8n1/ESP8266-Breakout-Adapter/Breakout Adapter v3/ESP Breakout Adapter v3.0A - AS1363 - Mini/ESP Breakout Adapter - v3_0A - AS1363 - Mini_sch.png

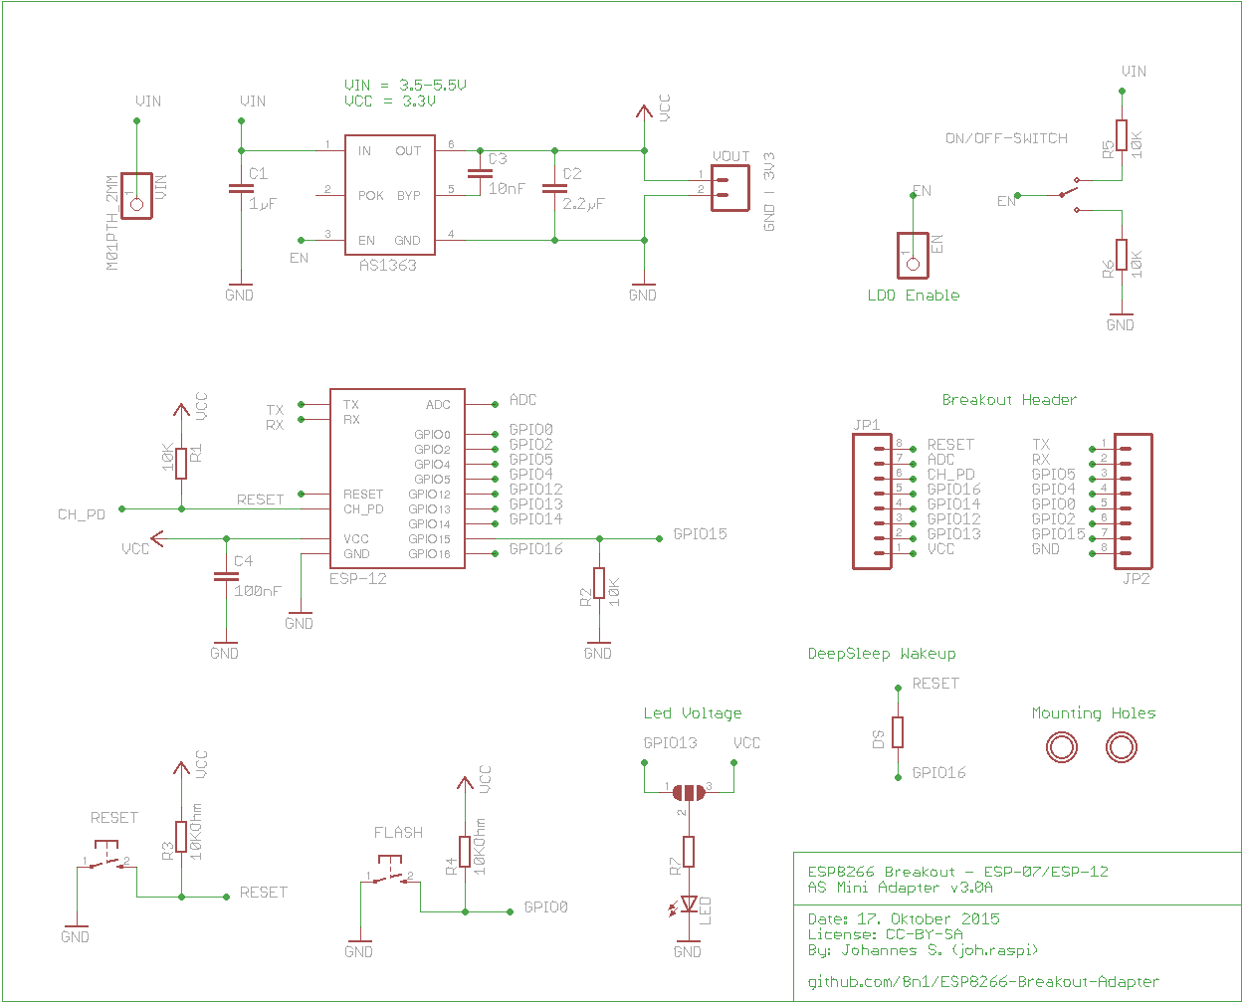
Breakout Adapter v3/ESP Breakout Adapter v3.0A - AS1363 - Mini/ESP Breakout Adapter - v3_0A - AS1363 - Mini_sch.png
