8n1/ESP8266-Breakout-Adapter/Breakout Adapter v3/ESP Breakout Adapter v3.0A - AS1363 - Mini/oshpark renderings/b_ohspark - board bottom_b.png

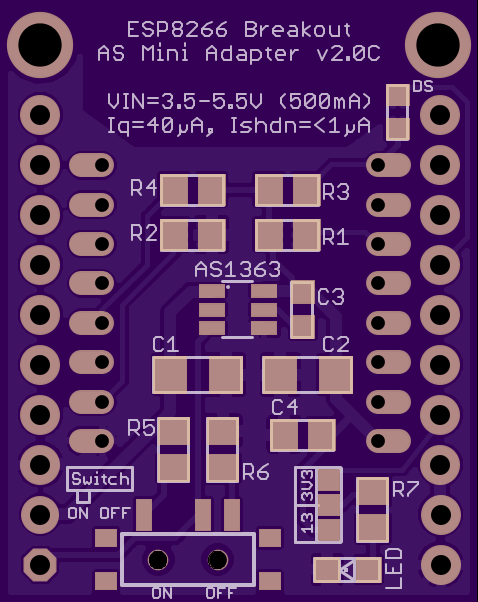
Breakout Adapter v3/ESP Breakout Adapter v3.0A - AS1363 - Mini/oshpark renderings/b_ohspark - board bottom_b.png
