8n1/ESP8266-Breakout-Adapter/Breakout Adapter v3/ESP Breakout Adapter v3.0A - AS1363 - Mini/oshpark renderings/oshpark - bottom layer.png

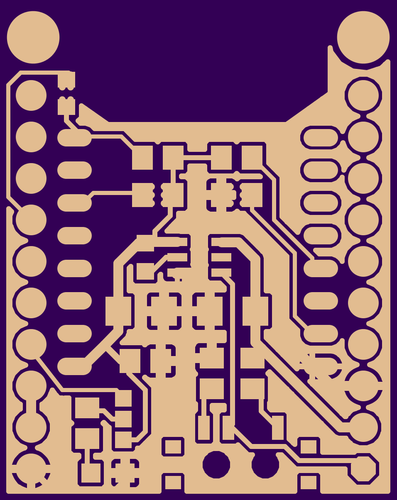
Breakout Adapter v3/ESP Breakout Adapter v3.0A - AS1363 - Mini/oshpark renderings/oshpark - bottom layer.png
