8n1/ESP8266-Breakout-Adapter/Breakout Adapter v3/ESP Breakout Adapter v3.1A - AS1363 - Mini/ESP Breakout Adapter - v3_1A - AS1363 - Mini_sch.png

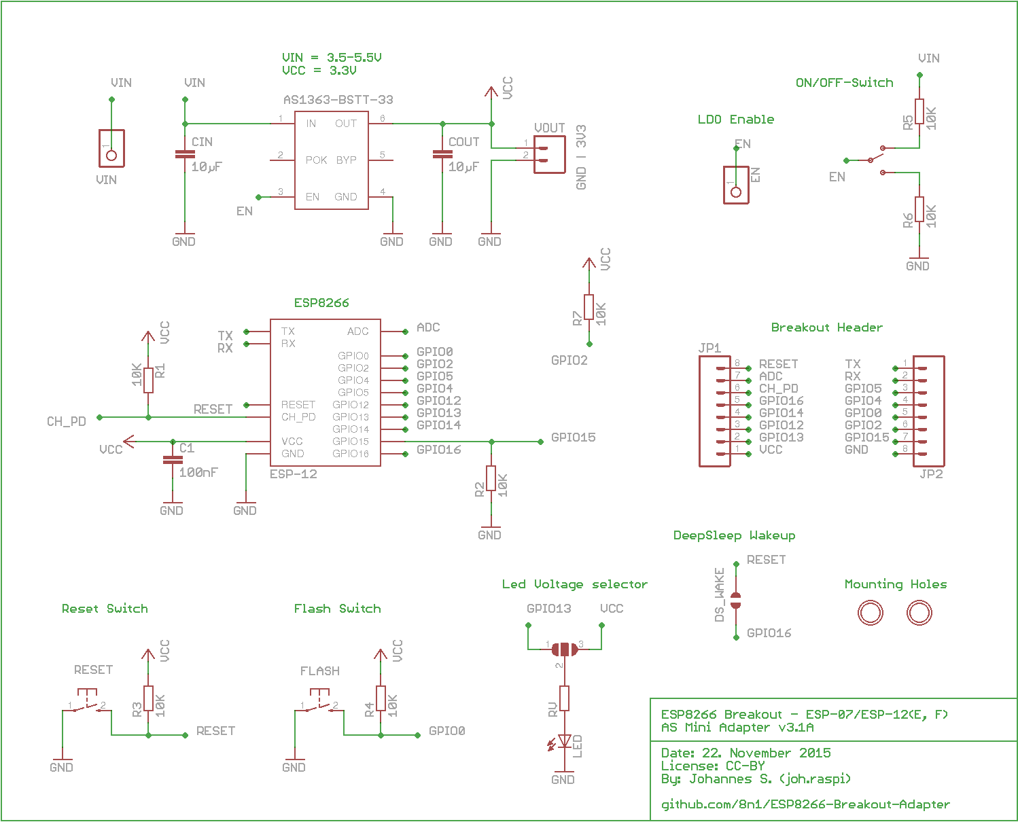
Breakout Adapter v3/ESP Breakout Adapter v3.1A - AS1363 - Mini/ESP Breakout Adapter - v3_1A - AS1363 - Mini_sch.png
