8n1/ESP8266-Breakout-Adapter/Breakout Adapter v3/ESP Breakout Adapter v3.1A - AS1363 - Mini/oshpark renderings/Board_Top.png

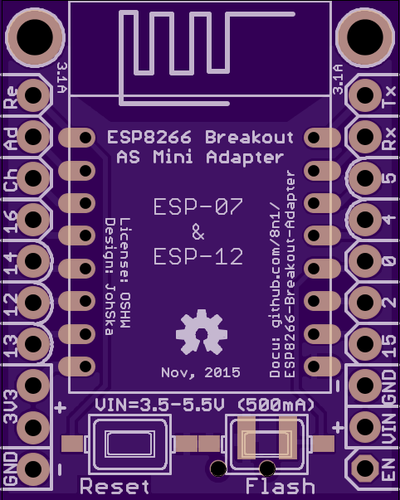
Breakout Adapter v3/ESP Breakout Adapter v3.1A - AS1363 - Mini/oshpark renderings/Board_Top.png
